Apoll011/Lambda-One/hardware/Lambda One.kicad_sch

## KiCad design hardware/Lambda One.kicad_sch (2026-07-18)

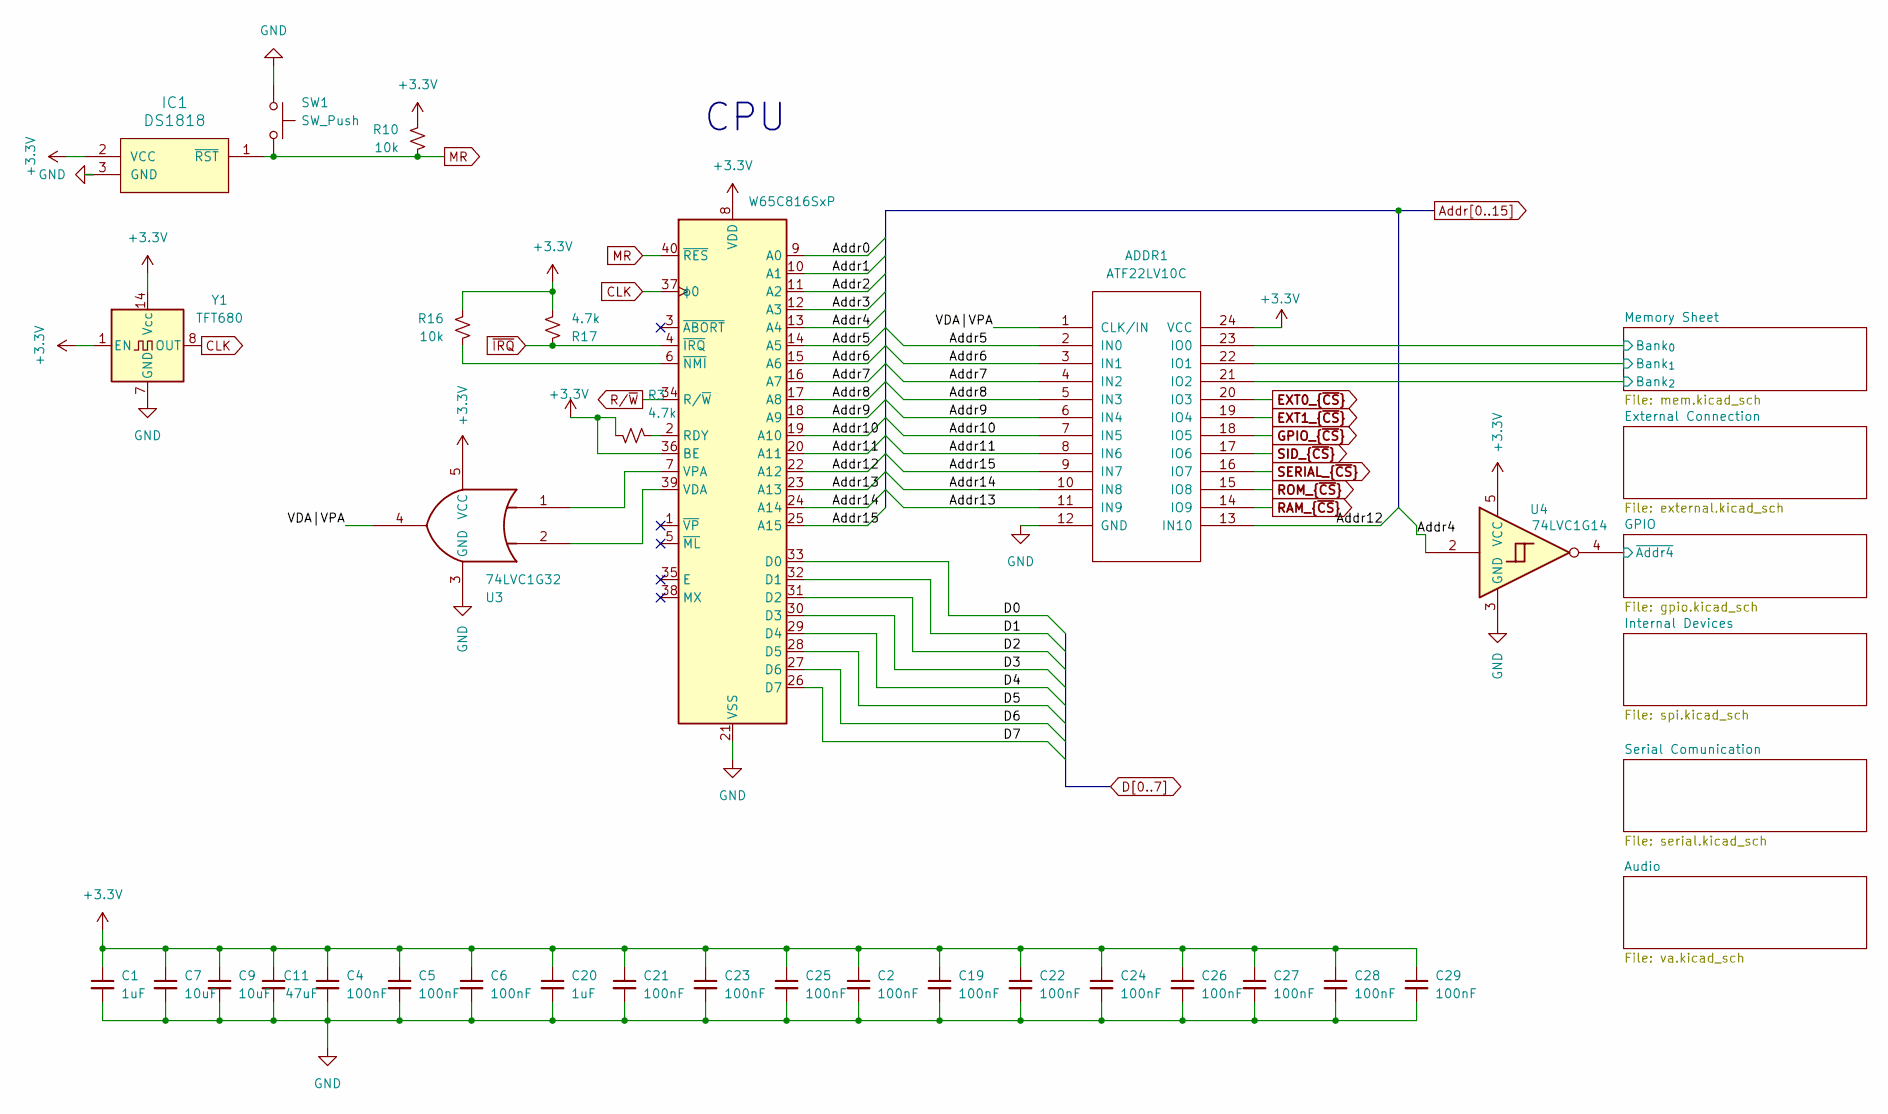
[picture p9: schematic Lambda One.kicad_sch]

Parts:
ADDR1: ATF22LV10C; DIP-24_W7.62mm
C1, C20: 1uF; C_0603_1608Metric; PartNumber CL10A105KB8NNNC
C2, C4, C5, C6, C19, C21, C22, C23, C24, C25, C26, C27, C28, C29: 100nF; C_0603_1608Metric; PartNumber CL10B104KB8NNNC
C7, C9: 10uF; C_0603_1608Metric; PartNumber CL10A105KB8NNNC
C11: 47uF; C_0603_1608Metric; PartNumber CL10A105KB8NNNC
CPU1: W65C816SxP; DIP-40_W15.24mm
IC1: DS1818; TO92127P495H695-3
R3, R17: 4.7k; R_0603_1608Metric; PartNumber AC0603JR-0710KL
R10, R16: 10k; R_0603_1608Metric; PartNumber AC0603JR-0710KL
SW1: SW_Push; SW_Push_1P1T_NO_CK_PTS125Sx73PSMTR
U3: 74LVC1G32; SOT-23-5
U4: 74LVC1G14; SOT-23-5
Y1: TFT680; Oscillator_DIP-14

Connections:
+3.3V: ADDR1.24 (VCC), C1.1, C2.1, C4.1, C5.1, C6.1, C7.1, C9.1, C11.1, C19.1, C20.1, C21.1, C22.1, C23.1, C24.1, C25.1, C26.1, C27.1, C28.1, C29.1, CPU1.8 (VDD), CPU1.36 (BE), IC1.2 (VCC), R3.2, R10.1, R16.1, R17.2, U3.5 (VCC), U4.5 (VCC), Y1.1 (EN), Y1.14 (Vcc)
Addr0: CPU1.9 (A0)
Addr1: CPU1.10 (A1)
Addr2: CPU1.11 (A2)
Addr3: CPU1.12 (A3)
Addr4: CPU1.13 (A4), U4.2
Addr5: ADDR1.2 (IN0), CPU1.14 (A5)
Addr6: ADDR1.3 (IN1), CPU1.15 (A6)
Addr7: ADDR1.4 (IN2), CPU1.16 (A7)
Addr8: ADDR1.5 (IN3), CPU1.17 (A8)
Addr9: ADDR1.6 (IN4), CPU1.18 (A9)
Addr10: ADDR1.7 (IN5), CPU1.19 (A10)
Addr11: ADDR1.8 (IN6), CPU1.20 (A11)
Addr12: ADDR1.13 (IN10), CPU1.22 (A12)
Addr13: ADDR1.11 (IN9), CPU1.23 (A13)
Addr14: ADDR1.10 (IN8), CPU1.24 (A14)
Addr15: ADDR1.9 (IN7), CPU1.25 (A15)
Bank_{0}: ADDR1.23 (IO0)
Bank_{1}: ADDR1.22 (IO1)
Bank_{2}: ADDR1.21 (IO2)
CLK: CPU1.37 (ϕ0), Y1.8 (OUT)
D0: CPU1.33 (D0)
D1: CPU1.32 (D1)
D2: CPU1.31 (D2)
D3: CPU1.30 (D3)
D4: CPU1.29 (D4)
D5: CPU1.28 (D5)
D6: CPU1.27 (D6)
D7: CPU1.26 (D7)
EXT0_{~CS}: ADDR1.20 (IO3)
EXT1_{~CS}: ADDR1.19 (IO4)
GND: ADDR1.12 (GND), C1.2, C2.2, C4.2, C5.2, C6.2, C7.2, C9.2, C11.2, C19.2, C20.2, C21.2, C22.2, C23.2, C24.2, C25.2, C26.2, C27.2, C28.2, C29.2, CPU1.21 (VSS), IC1.3 (GND), SW1.1, U3.3 (GND), U4.3 (GND), Y1.7 (GND)
GPIO_{~CS}: ADDR1.18 (IO5)
MR: CPU1.40 (~RES), IC1.1 (~RST), R10.2, SW1.2
unnamed: CPU1.2 (RDY), R3.1
unnamed: CPU1.6 (~NMI), R16.2
unnamed: CPU1.7 (VPA), U3.1
unnamed: CPU1.39 (VDA), U3.2
RAM_{~CS}: ADDR1.14 (IO9)
ROM_{~CS}: ADDR1.15 (IO8)
R/~W: CPU1.34 (R/~W)
SERIAL_{~CS}: ADDR1.16 (IO7)
SID_{~CS}: ADDR1.17 (IO6)
VDA|VPA: ADDR1.1 (CLK/IN), U3.4
~Addr4: U4.4
~IRQ: CPU1.4 (~IRQ), R17.1

Notes on the sheet:
CPU
