Apoll011/Lambda-One/hardware/ethernet.kicad_sch

## KiCad design hardware/ethernet.kicad_sch (2026-07-13)

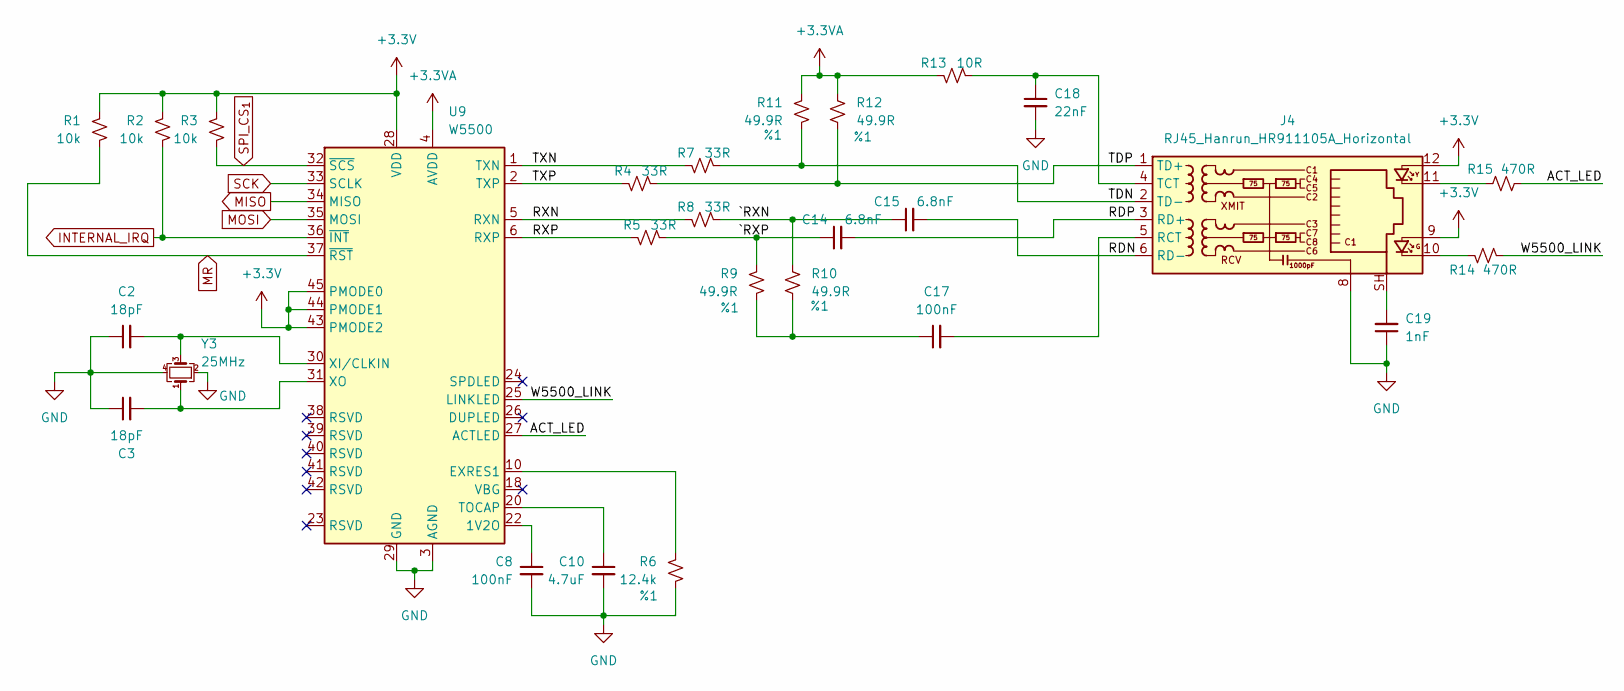
[picture p10: schematic ethernet.kicad_sch]

Parts:
C2, C3: 18pF; C_0603_1608Metric; PartNumber CC0603JRNPO9BN180
C8, C17: 100nF; C_0603_1608Metric; PartNumber CL10B104KB8NNNC
C10: 4.7uF; C_0603_1608Metric; PartNumber CL10B475KQ8NQNC
C14, C15: 6.8nF; C_0603_1608Metric; PartNumber CL10B682KB8NNNC
C18: 22nF; C_0603_1608Metric; PartNumber CL10B223KB8NNNC
C19: 1nF; C_1210_3225Metric; PartNumber CL32B102KJFNNNE
J4: RJ45_Hanrun_HR911105A_Horizontal; PartNumber HR911105A
R1, R2, R3: 10k; R_0603_1608Metric; PartNumber AC0603JR-0710KL
R4, R5, R7, R8: 33R; R_0603_1608Metric; PartNumber RC0603JR-0733RL
R6: 12.4k; R_0603_1608Metric; Tolerance %1; PartNumber RC0603FR-0712K4L
R9, R10, R11, R12: 49.9R; R_0603_1608Metric; Tolerance %1; PartNumber ERA-3AEB49R9V
R13: 10R; R_0603_1608Metric; PartNumber RC0603FR-0710RL
R14, R15: 470R; R_0603_1608Metric; PartNumber RC0603JR-07470RL
U9: W5500; LQFP-48_7x7mm_P0.5mm; PartNumber W5500
Y3: 25MHz; Crystal_SMD_Abracon_ABM8AIG-4Pin_3.2x2.5mm; PartNumber RH100-25.000-10-F-2030-E

Connections:
+3.3V: J4.9, J4.12, R1.1, R2.1, R3.1, U9.28 (VDD), U9.43 (PMODE2), U9.44 (PMODE1), U9.45 (PMODE0)
+3.3VA: R11.1, R12.1, R13.1, U9.4 (AVDD), U9.8 (AVDD), U9.11 (AVDD), U9.15 (AVDD), U9.17 (AVDD), U9.21 (AVDD)
ACT_LED: R15.2, U9.27 (ACTLED)
GND: C2.1, C3.1, C8.2, C10.2, C18.2, C19.1, J4.8, R6.2, U9.3 (AGND), U9.9 (AGND), U9.14 (AGND), U9.16 (AGND), U9.19 (AGND), U9.29 (GND), U9.48 (AGND), Y3.2, Y3.4
INTERNAL_IRQ: R2.2, U9.36 (~INT)
MISO: U9.34 (MISO)
MOSI: U9.35 (MOSI)
MR: R1.2, U9.37 (~RST)
unnamed: C2.2, U9.30 (XI/CLKIN), Y3.3
unnamed: C3.2, U9.31 (XO), Y3.1
unnamed: C8.1, U9.22 (1V2O)
unnamed: C10.1, U9.20 (TOCAP)
unnamed: C17.1, R9.2, R10.2
unnamed: C17.2, J4.5 (RCT)
unnamed: C18.1, J4.4 (TCT), R13.2
unnamed: C19.2, J4.SH
unnamed: J4.10, R14.1
unnamed: J4.11, R15.1
unnamed: R6.1, U9.10 (EXRES1)
RDN: C15.2, J4.6 (RD-)
RDP: C14.2, J4.3 (RD+)
RXN: R8.1, U9.5 (RXN)
RXP: R5.1, U9.6 (RXP)
SCK: U9.33 (SCLK)
SPI_CS_{1}: R3.2, U9.32 (~SCS)
TDN: J4.2 (TD-), R7.2, R11.2
TDP: J4.1 (TD+), R4.2, R12.2
TXN: R7.1, U9.1 (TXN)
TXP: R4.1, U9.2 (TXP)
W5500_LINK: R14.2, U9.25 (LINKLED)
`RXN: C15.1, R8.2, R10.1
`RXP: C14.1, R5.2, R9.1
