Apoll011/Lambda-One/hardware/external.kicad_sch

## KiCad design hardware/external.kicad_sch (2026-07-18)

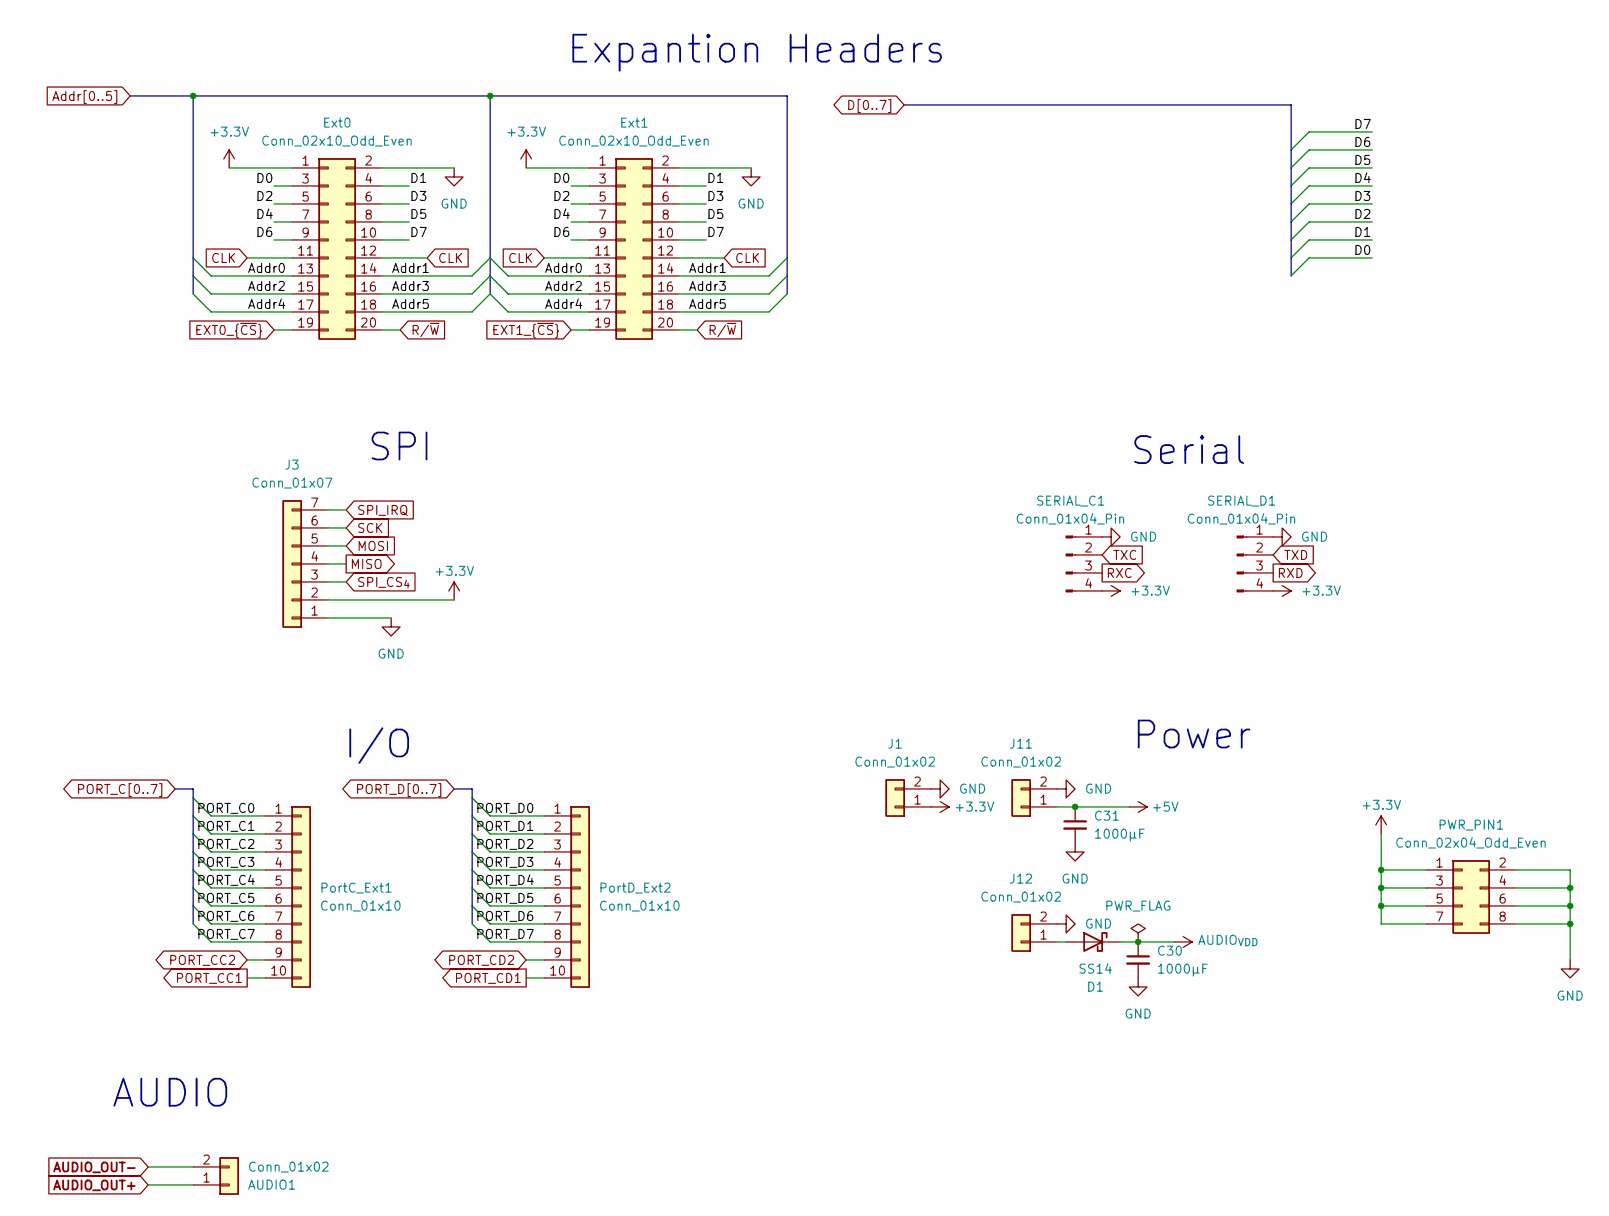
[picture p11: schematic external.kicad_sch]

Parts:
AUDIO1: Conn_01x02; JST_XH_B2B-XH-A_1x02_P2.50mm_Vertical
C30, C31: 1000µF; Fuse_Bourns_MF-RG1000; PartNumber CL10B104KB8NNNC
D1: SS14; D_SMA
Ext0, Ext1: Conn_02x10_Odd_Even; IDC-Header_2x10_P2.54mm_Vertical
J1, J11, J12: Conn_01x02; JST_XH_B2B-XH-A_1x02_P2.50mm_Vertical
J3: Conn_01x07; PinHeader_1x07_P2.54mm_Vertical
PWR_PIN1: Conn_02x04_Odd_Even; PinHeader_2x04_P2.54mm_Vertical
PortC_Ext1: Conn_01x10; PinHeader_1x10_P2.54mm_Vertical
PortD_Ext2: Conn_01x10; PinHeader_1x10_P2.54mm_Vertical
SERIAL_C1: Conn_01x04_Pin; PinHeader_1x04_P2.54mm_Vertical
SERIAL_D1: Conn_01x04_Pin; PinHeader_1x04_P2.54mm_Vertical

Connections:
+3.3V: Ext0.1, Ext1.1, J1.1, J3.2, PWR_PIN1.1, PWR_PIN1.3, PWR_PIN1.5, PWR_PIN1.7, SERIAL_C1.4, SERIAL_D1.4
+5V: C31.1, J11.1
AUDIO_OUT+: AUDIO1.1
AUDIO_OUT-: AUDIO1.2
AUDIO_{VDD}: C30.1, D1.1 (K)
Addr0: Ext0.13, Ext1.13
Addr1: Ext0.14, Ext1.14
Addr2: Ext0.15, Ext1.15
Addr3: Ext0.16, Ext1.16
Addr4: Ext0.17, Ext1.17
Addr5: Ext0.18, Ext1.18
CLK: Ext0.11, Ext0.12, Ext1.11, Ext1.12
D0: Ext0.3, Ext1.3
D1: Ext0.4, Ext1.4
D2: Ext0.5, Ext1.5
D3: Ext0.6, Ext1.6
D4: Ext0.7, Ext1.7
D5: Ext0.8, Ext1.8
D6: Ext0.9, Ext1.9
D7: Ext0.10, Ext1.10
EXT0_{~CS}: Ext0.19
EXT1_{~CS}: Ext1.19
GND: C30.2, C31.2, Ext0.2, Ext1.2, J1.2, J3.1, J11.2, J12.2, PWR_PIN1.2, PWR_PIN1.4, PWR_PIN1.6, PWR_PIN1.8, SERIAL_C1.1, SERIAL_D1.1
MISO: J3.4
MOSI: J3.5
unnamed: D1.2 (A), J12.1
PORT_C0: PortC_Ext1.1
PORT_C1: PortC_Ext1.2
PORT_C2: PortC_Ext1.3
PORT_C3: PortC_Ext1.4
PORT_C4: PortC_Ext1.5
PORT_C5: PortC_Ext1.6
PORT_C6: PortC_Ext1.7
PORT_C7: PortC_Ext1.8
PORT_CC1: PortC_Ext1.10
PORT_CC2: PortC_Ext1.9
PORT_CD1: PortD_Ext2.10
PORT_CD2: PortD_Ext2.9
PORT_D0: PortD_Ext2.1
PORT_D1: PortD_Ext2.2
PORT_D2: PortD_Ext2.3
PORT_D3: PortD_Ext2.4
PORT_D4: PortD_Ext2.5
PORT_D5: PortD_Ext2.6
PORT_D6: PortD_Ext2.7
PORT_D7: PortD_Ext2.8
RXC: SERIAL_C1.3
RXD: SERIAL_D1.3
R/~W: Ext0.20, Ext1.20
SCK: J3.6
SPI_CS_{4}: J3.3
SPI_IRQ: J3.7
TXC: SERIAL_C1.2
TXD: SERIAL_D1.2

Notes on the sheet:
Power
SPI
Expantion Headers
Serial
I/O
AUDIO
