Apoll011/Lambda-One/hardware/gpio.kicad_sch

## KiCad design hardware/gpio.kicad_sch (2026-07-18)

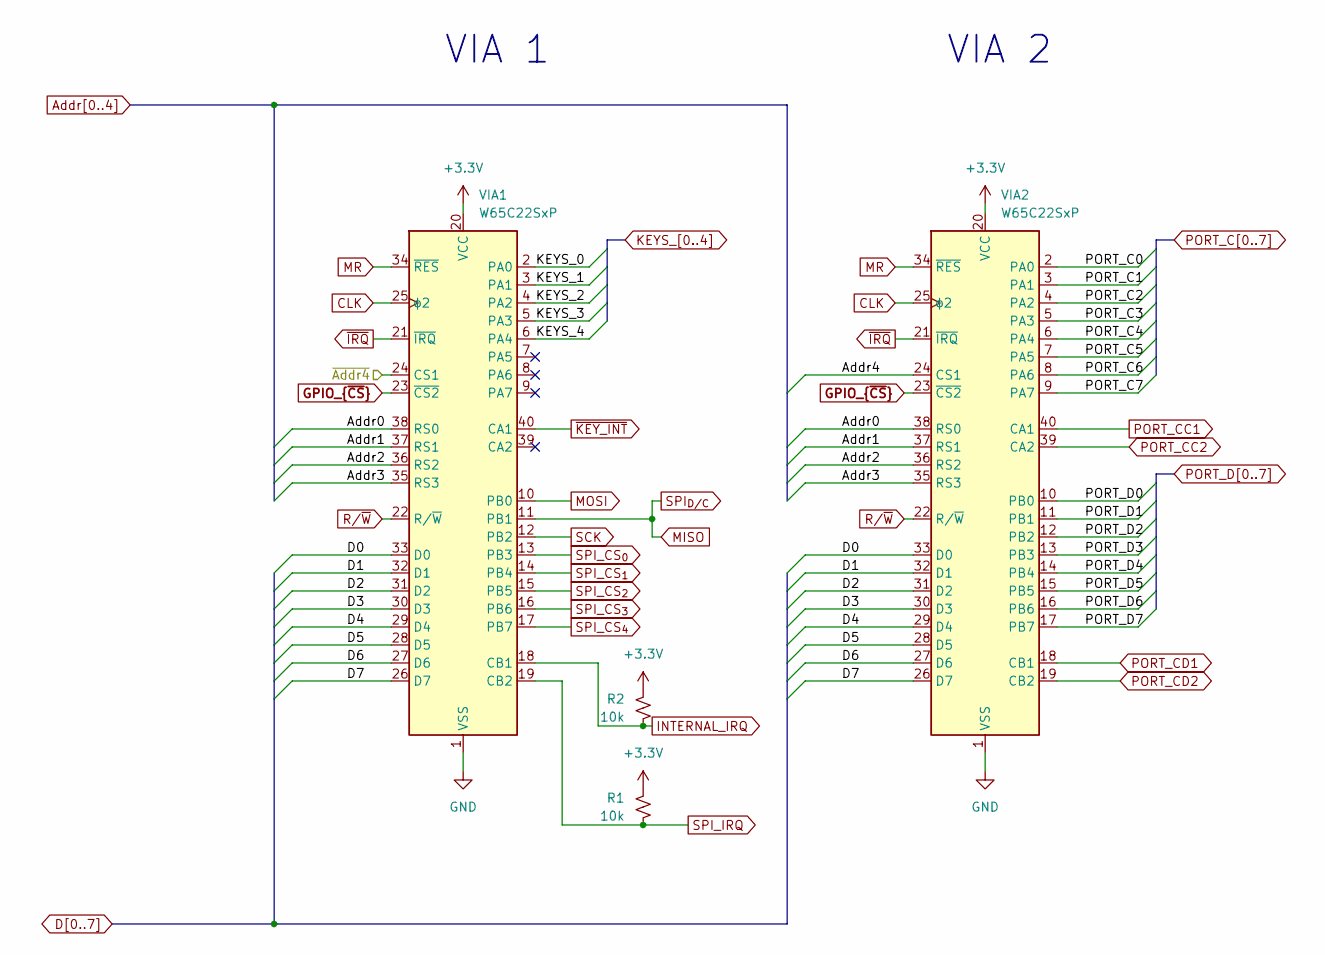
[picture p12: schematic gpio.kicad_sch]

Parts:
R1, R2: 10k; R_0603_1608Metric; PartNumber AC0603JR-0710KL
VIA1, VIA2: W65C22SxP; DIP-40_W15.24mm

Connections:
+3.3V: R1.1, R2.1, VIA1.20 (VCC), VIA2.20 (VCC)
Addr0: VIA1.38 (RS0), VIA2.38 (RS0)
Addr1: VIA1.37 (RS1), VIA2.37 (RS1)
Addr2: VIA1.36 (RS2), VIA2.36 (RS2)
Addr3: VIA1.35 (RS3), VIA2.35 (RS3)
Addr4: VIA2.24 (CS1)
CLK: VIA1.25 (ϕ2), VIA2.25 (ϕ2)
D0: VIA1.33 (D0), VIA2.33 (D0)
D1: VIA1.32 (D1), VIA2.32 (D1)
D2: VIA1.31 (D2), VIA2.31 (D2)
D3: VIA1.30 (D3), VIA2.30 (D3)
D4: VIA1.29 (D4), VIA2.29 (D4)
D5: VIA1.28 (D5), VIA2.28 (D5)
D6: VIA1.27 (D6), VIA2.27 (D6)
D7: VIA1.26 (D7), VIA2.26 (D7)
GND: VIA1.1 (VSS), VIA2.1 (VSS)
GPIO_{~CS}: VIA1.23 (~CS2), VIA2.23 (~CS2)
INTERNAL_IRQ: R2.2, VIA1.18 (CB1)
KEYS_0: VIA1.2 (PA0)
KEYS_1: VIA1.3 (PA1)
KEYS_2: VIA1.4 (PA2)
KEYS_3: VIA1.5 (PA3)
KEYS_4: VIA1.6 (PA4)
MISO: VIA1.11 (PB1)
MOSI: VIA1.10 (PB0)
MR: VIA1.34 (~RES), VIA2.34 (~RES)
PORT_C0: VIA2.2 (PA0)
PORT_C1: VIA2.3 (PA1)
PORT_C2: VIA2.4 (PA2)
PORT_C3: VIA2.5 (PA3)
PORT_C4: VIA2.6 (PA4)
PORT_C5: VIA2.7 (PA5)
PORT_C6: VIA2.8 (PA6)
PORT_C7: VIA2.9 (PA7)
PORT_CC1: VIA2.40 (CA1)
PORT_CC2: VIA2.39 (CA2)
PORT_CD1: VIA2.18 (CB1)
PORT_CD2: VIA2.19 (CB2)
PORT_D0: VIA2.10 (PB0)
PORT_D1: VIA2.11 (PB1)
PORT_D2: VIA2.12 (PB2)
PORT_D3: VIA2.13 (PB3)
PORT_D4: VIA2.14 (PB4)
PORT_D5: VIA2.15 (PB5)
PORT_D6: VIA2.16 (PB6)
PORT_D7: VIA2.17 (PB7)
R/~W: VIA1.22 (R/~W), VIA2.22 (R/~W)
SCK: VIA1.12 (PB2)
SPI_CS_{0}: VIA1.13 (PB3)
SPI_CS_{1}: VIA1.14 (PB4)
SPI_CS_{2}: VIA1.15 (PB5)
SPI_CS_{3}: VIA1.16 (PB6)
SPI_CS_{4}: VIA1.17 (PB7)
SPI_IRQ: R1.2, VIA1.19 (CB2)
~Addr4: VIA1.24 (CS1)
~IRQ: VIA1.21 (~IRQ), VIA2.21 (~IRQ)
~KEY_INT: VIA1.40 (CA1)

Notes on the sheet:
VIA 1
VIA 2
