Apoll011/Lambda-One/hardware/interface.kicad_sch

## KiCad design hardware/interface.kicad_sch (2026-07-13)

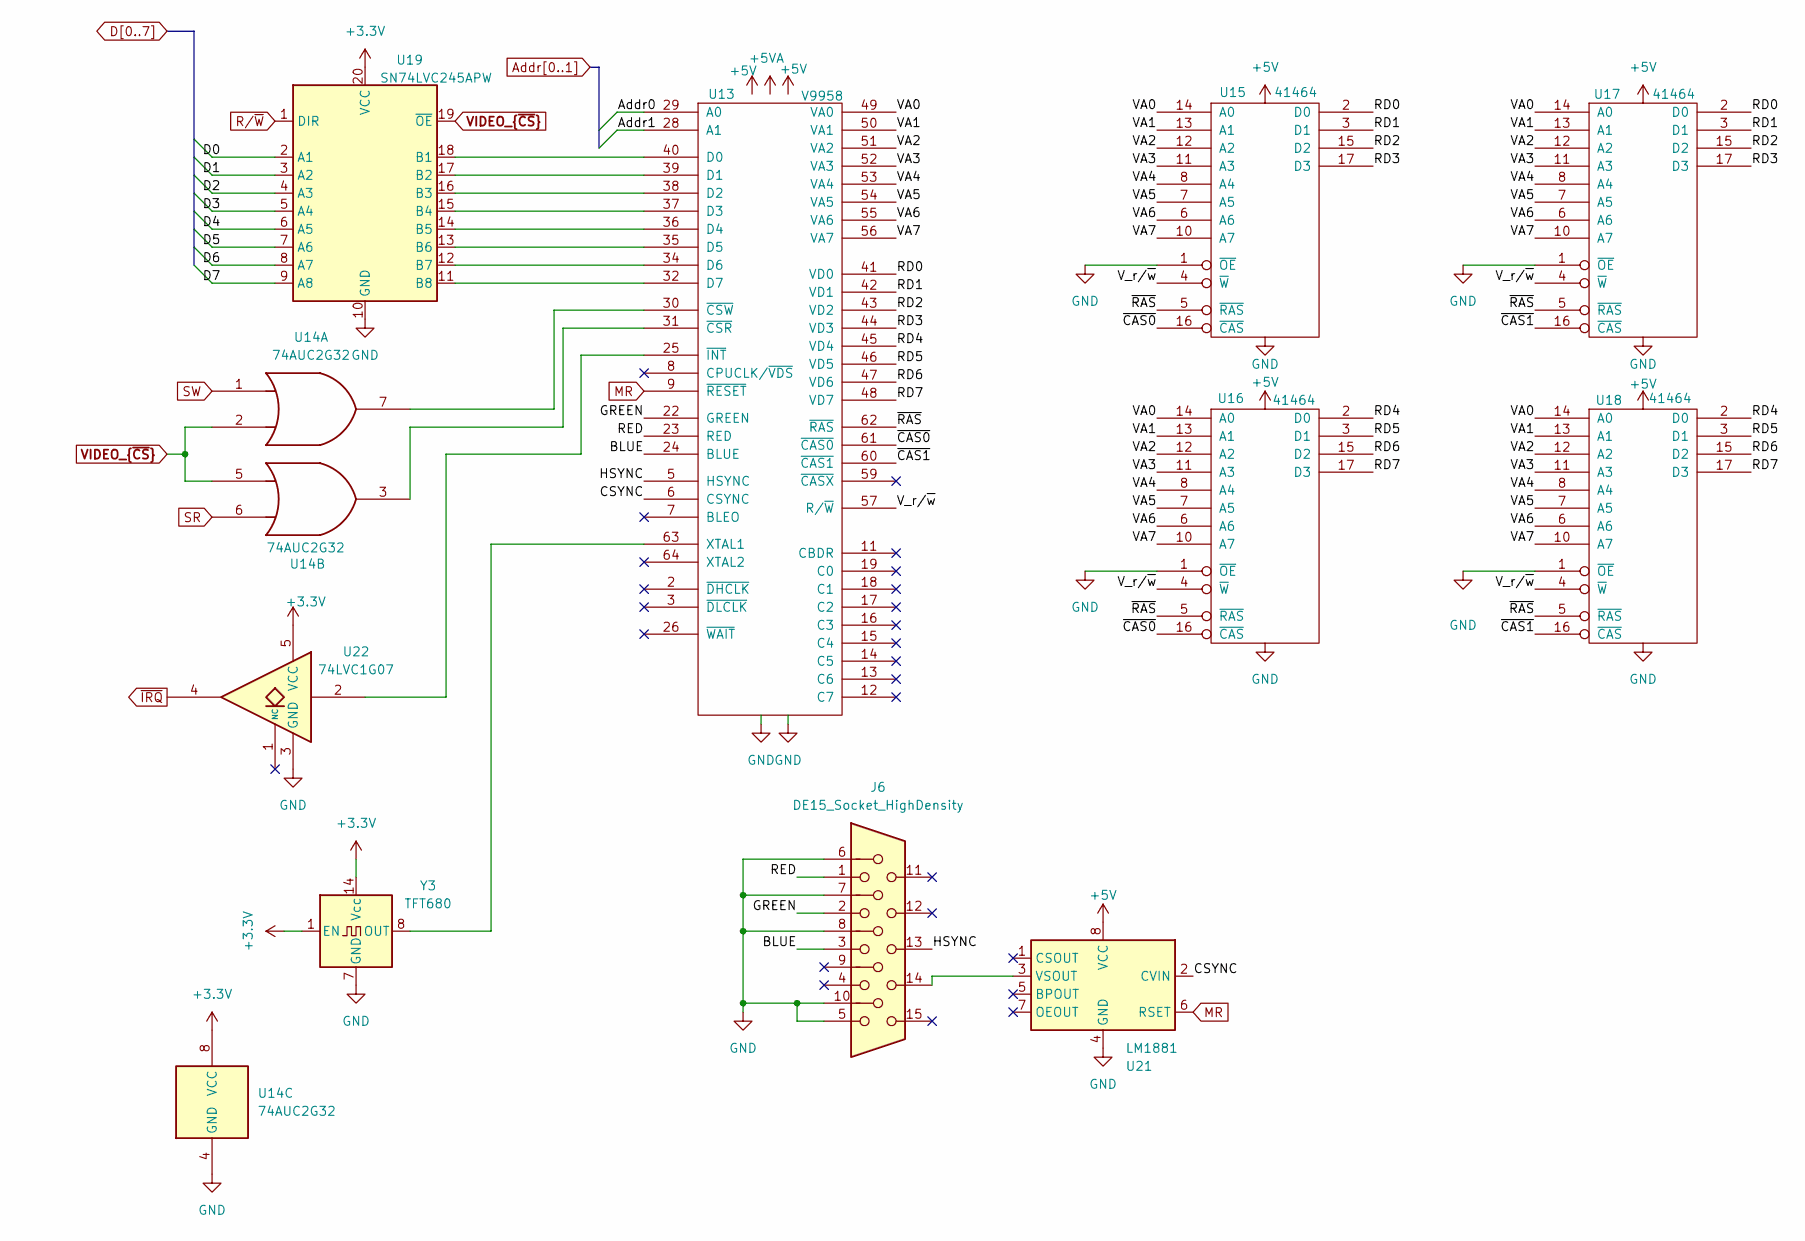
[picture p13: schematic interface.kicad_sch]

Parts:
J6: DE15_Socket_HighDensity
U13: V9958
U14: 74AUC2G32
U15, U16, U17, U18: 41464
U19: SN74LVC245APW; TSSOP-20_4.4x6.5mm_P0.65mm
U21: LM1881
U22: 74LVC1G07
Y3: TFT680; Oscillator_DIP-14

Connections:
+3.3V: U14.8 (VCC), U19.20 (VCC), U22.5 (VCC), Y3.1 (EN), Y3.14 (Vcc)
+5V: U13.33 (Vbb), U13.58 (VCC), U15.9 (VCC), U16.9 (VCC), U17.9 (VCC), U18.9 (VCC), U21.8 (VCC)
+5VA: U13.21 (VDD)
Addr0: U13.29 (A0)
Addr1: U13.28 (A1)
BLUE: J6.3, U13.24 (BLUE)
CSYNC: U13.6 (CSYNC), U21.2 (CVIN)
D0: U19.2 (A1)
D1: U19.3 (A2)
D2: U19.4 (A3)
D3: U19.5 (A4)
D4: U19.6 (A5)
D5: U19.7 (A6)
D6: U19.8 (A7)
D7: U19.9 (A8)
GND: J6.5, J6.6, J6.7, J6.8, J6.10, U13.1 (GND), U13.20 (GND), U14.4 (GND), U15.1 (~OE), U15.18 (GND), U16.1 (~OE), U16.18 (GND), U17.1 (~OE), U17.18 (GND), U18.1 (~OE), U18.18 (GND), U19.10 (GND), U21.4 (GND), U22.3 (GND), Y3.7 (GND)
GREEN: J6.2, U13.22 (GREEN)
HSYNC: J6.13, U13.5 (HSYNC)
MR: U13.9 (~RESET), U21.6 (RSET)
unnamed: J6.14, U21.3 (VSOUT)
unnamed: U13.25 (~INT), U22.2
unnamed: U13.30 (~CSW), U14.7
unnamed: U13.31 (~CSR), U14.3
unnamed: U13.32 (D7), U19.11 (B8)
unnamed: U13.34 (D6), U19.12 (B7)
unnamed: U13.35 (D5), U19.13 (B6)
unnamed: U13.36 (D4), U19.14 (B5)
unnamed: U13.37 (D3), U19.15 (B4)
unnamed: U13.38 (D2), U19.16 (B3)
unnamed: U13.39 (D1), U19.17 (B2)
unnamed: U13.40 (D0), U19.18 (B1)
unnamed: U13.63 (XTAL1), Y3.8 (OUT)
RD0: U13.41 (VD0), U15.2 (D0), U17.2 (D0)
RD1: U13.42 (VD1), U15.3 (D1), U17.3 (D1)
RD2: U13.43 (VD2), U15.15 (D2), U17.15 (D2)
RD3: U13.44 (VD3), U15.17 (D3), U17.17 (D3)
RD4: U13.45 (VD4), U16.2 (D0), U18.2 (D0)
RD5: U13.46 (VD5), U16.3 (D1), U18.3 (D1)
RD6: U13.47 (VD6), U16.15 (D2), U18.15 (D2)
RD7: U13.48 (VD7), U16.17 (D3), U18.17 (D3)
RED: J6.1, U13.23 (RED)
R/~W: U19.1 (DIR)
SR: U14.6
SW: U14.1
VA0: U13.49 (VA0), U15.14 (A0), U16.14 (A0), U17.14 (A0), U18.14 (A0)
VA1: U13.50 (VA1), U15.13 (A1), U16.13 (A1), U17.13 (A1), U18.13 (A1)
VA2: U13.51 (VA2), U15.12 (A2), U16.12 (A2), U17.12 (A2), U18.12 (A2)
VA3: U13.52 (VA3), U15.11 (A3), U16.11 (A3), U17.11 (A3), U18.11 (A3)
VA4: U13.53 (VA4), U15.8 (A4), U16.8 (A4), U17.8 (A4), U18.8 (A4)
VA5: U13.54 (VA5), U15.7 (A5), U16.7 (A5), U17.7 (A5), U18.7 (A5)
VA6: U13.55 (VA6), U15.6 (A6), U16.6 (A6), U17.6 (A6), U18.6 (A6)
VA7: U13.56 (VA7), U15.10 (A7), U16.10 (A7), U17.10 (A7), U18.10 (A7)
VIDEO_{~CS}: U14.2, U14.5, U19.19 (~OE)
V_r/~w: U13.57 (R/~W), U15.4 (~W), U16.4 (~W), U17.4 (~W), U18.4 (~W)
~CAS0: U13.61 (~CAS0), U15.16 (~CAS), U16.16 (~CAS)
~CAS1: U13.60 (~CAS1), U17.16 (~CAS), U18.16 (~CAS)
~IRQ: U22.4
~RAS: U13.62 (~RAS), U15.5 (~RAS), U16.5 (~RAS), U17.5 (~RAS), U18.5 (~RAS)
