Apoll011/Lambda-One/hardware/mem.kicad_sch

## KiCad design hardware/mem.kicad_sch (2026-07-18)

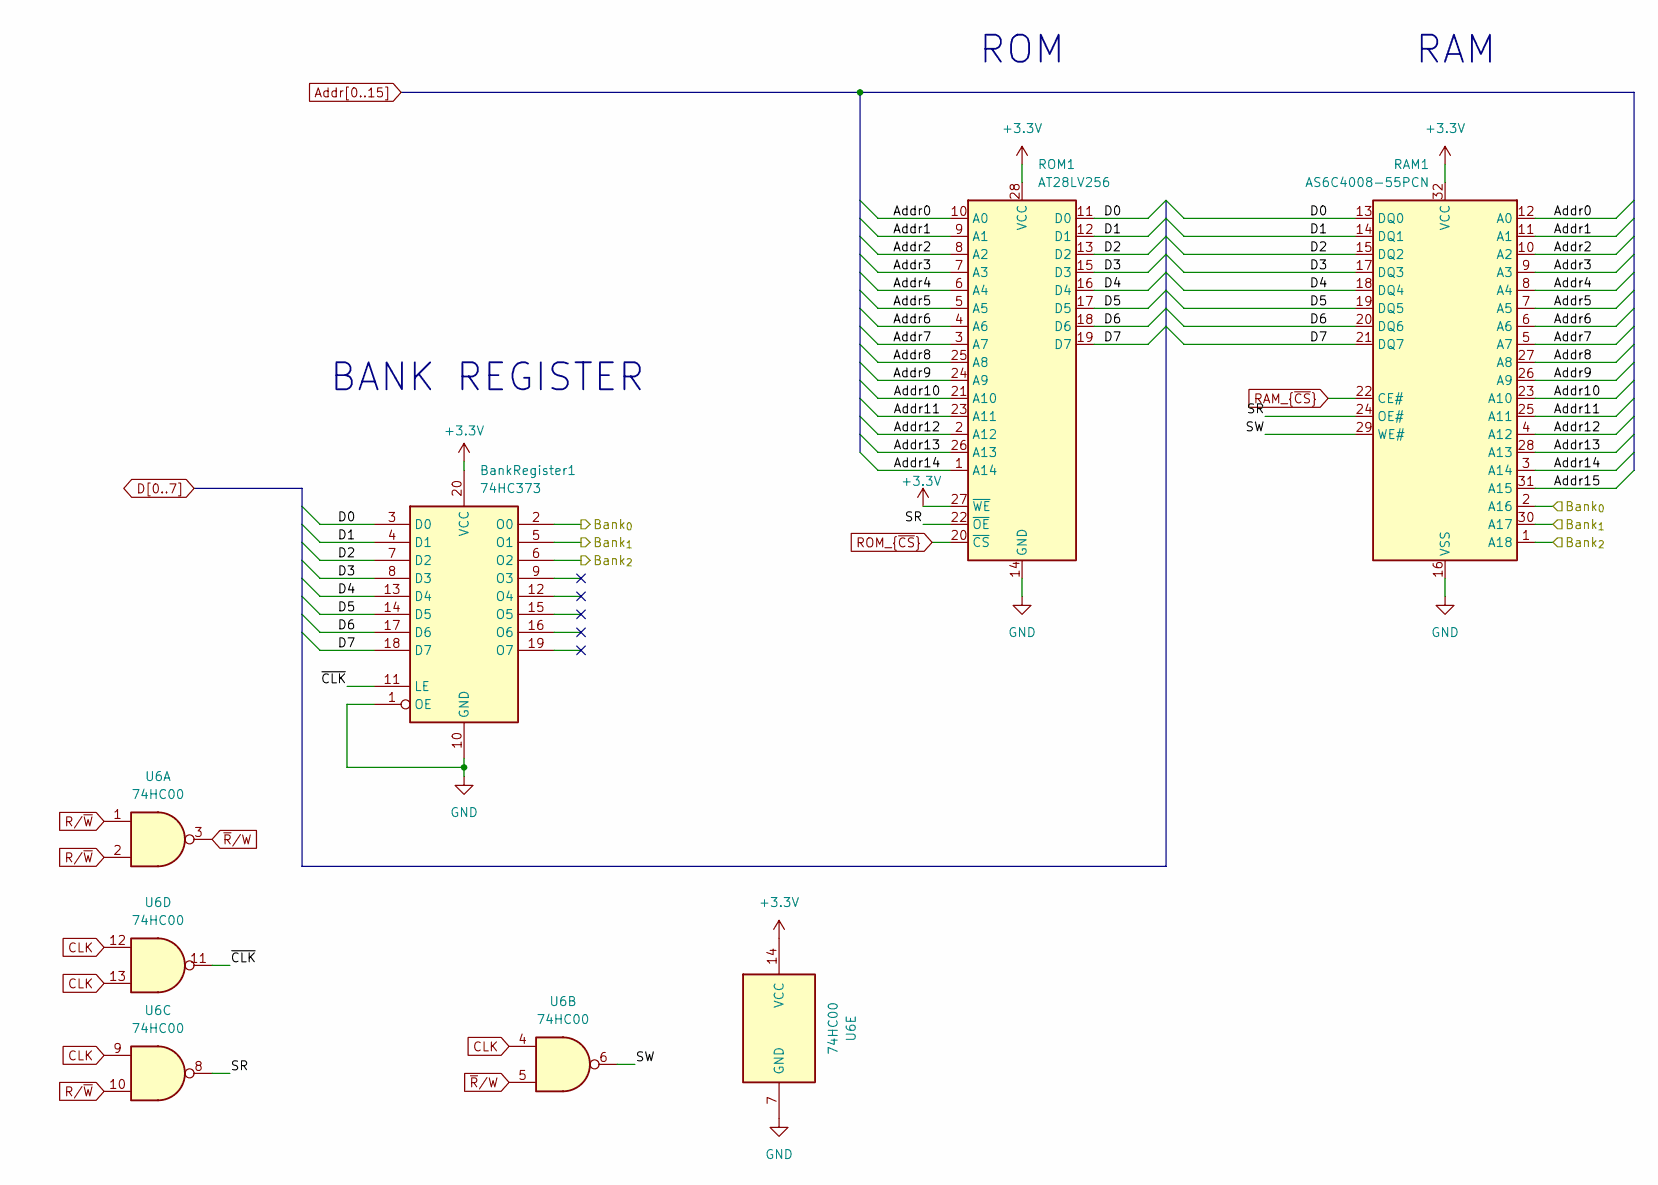
[picture p14: schematic mem.kicad_sch]

Parts:
BankRegister1: 74HC373; DIP-20_W7.62mm
RAM1: AS6C4008-55PCN; DIP-32_W15.24mm
ROM1: AT28LV256; DIP-28_W15.24mm_Socket
U6: 74HC00; DIP-14_W7.62mm

Connections:
+3.3V: BankRegister1.20 (VCC), RAM1.32 (VCC), ROM1.27 (~WE), ROM1.28 (VCC), U6.14 (VCC)
Addr0: RAM1.12 (A0), ROM1.10 (A0)
Addr1: RAM1.11 (A1), ROM1.9 (A1)
Addr2: RAM1.10 (A2), ROM1.8 (A2)
Addr3: RAM1.9 (A3), ROM1.7 (A3)
Addr4: RAM1.8 (A4), ROM1.6 (A4)
Addr5: RAM1.7 (A5), ROM1.5 (A5)
Addr6: RAM1.6 (A6), ROM1.4 (A6)
Addr7: RAM1.5 (A7), ROM1.3 (A7)
Addr8: RAM1.27 (A8), ROM1.25 (A8)
Addr9: RAM1.26 (A9), ROM1.24 (A9)
Addr10: RAM1.23 (A10), ROM1.21 (A10)
Addr11: RAM1.25 (A11), ROM1.23 (A11)
Addr12: RAM1.4 (A12), ROM1.2 (A12)
Addr13: RAM1.28 (A13), ROM1.26 (A13)
Addr14: RAM1.3 (A14), ROM1.1 (A14)
Addr15: RAM1.31 (A15)
Bank_{0}: BankRegister1.2 (O0), RAM1.2 (A16)
Bank_{1}: BankRegister1.5 (O1), RAM1.30 (A17)
Bank_{2}: BankRegister1.6 (O2), RAM1.1 (A18)
CLK: U6.4, U6.9, U6.12, U6.13
D0: BankRegister1.3 (D0), RAM1.13 (DQ0), ROM1.11 (D0)
D1: BankRegister1.4 (D1), RAM1.14 (DQ1), ROM1.12 (D1)
D2: BankRegister1.7 (D2), RAM1.15 (DQ2), ROM1.13 (D2)
D3: BankRegister1.8 (D3), RAM1.17 (DQ3), ROM1.15 (D3)
D4: BankRegister1.13 (D4), RAM1.18 (DQ4), ROM1.16 (D4)
D5: BankRegister1.14 (D5), RAM1.19 (DQ5), ROM1.17 (D5)
D6: BankRegister1.17 (D6), RAM1.20 (DQ6), ROM1.18 (D6)
D7: BankRegister1.18 (D7), RAM1.21 (DQ7), ROM1.19 (D7)
GND: BankRegister1.1 (OE), BankRegister1.10 (GND), RAM1.16 (VSS), ROM1.14 (GND), U6.7 (GND)
RAM_{~CS}: RAM1.22 (CE#)
ROM_{~CS}: ROM1.20 (~CS)
R/~W: U6.1, U6.2, U6.10
SR: RAM1.24 (OE#), ROM1.22 (~OE), U6.8
SW: RAM1.29 (WE#), U6.6
~CLK: BankRegister1.11 (LE), U6.11
~R/W: U6.3, U6.5

Notes on the sheet:
RAM
BANK REGISTER
ROM
