Apoll011/Lambda-One/hardware/serial.kicad_sch

## KiCad design hardware/serial.kicad_sch (2026-07-18)

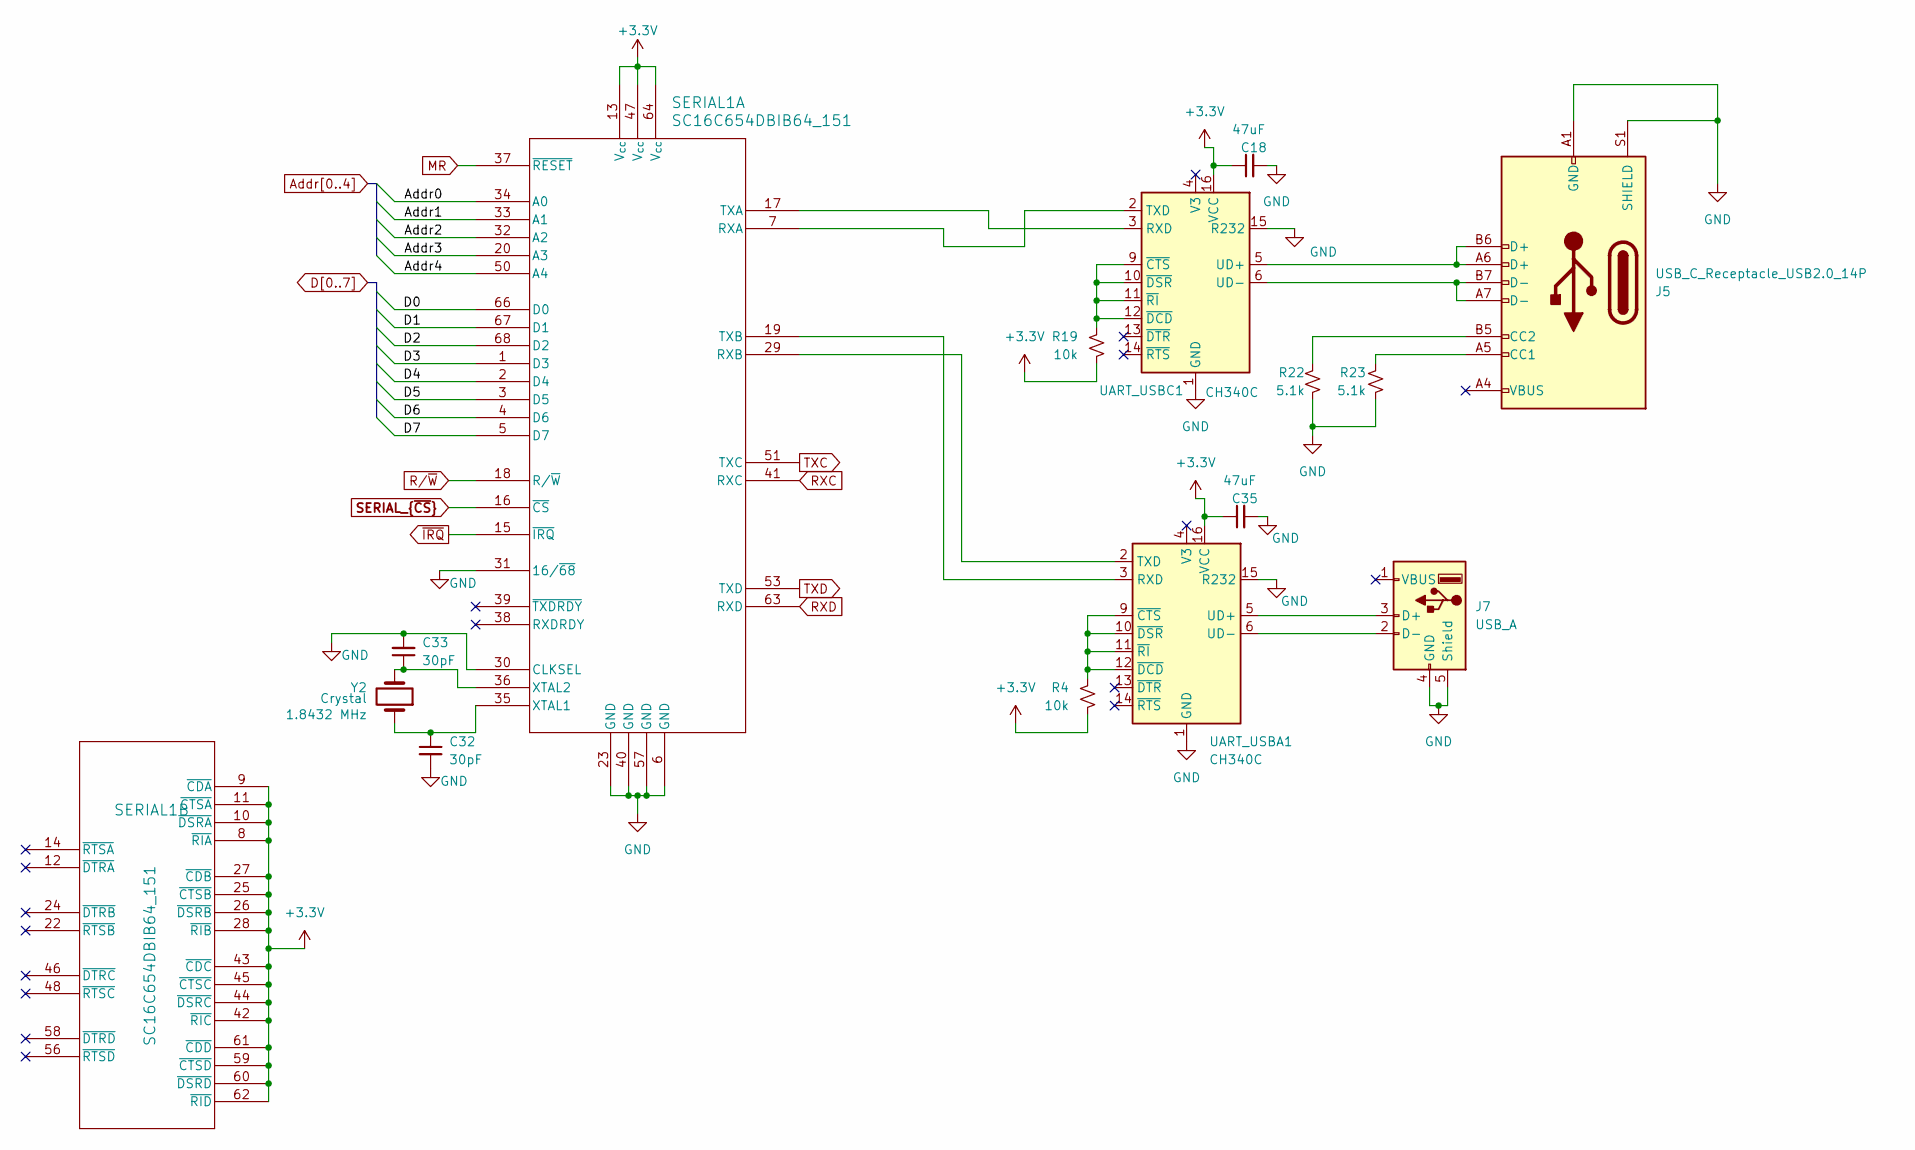
[picture p15: schematic serial.kicad_sch]

Parts:
C18, C35: 47uF; C_0603_1608Metric; PartNumber CL10A105KB8NNNC
C32, C33: 30pF; C_0603_1608Metric; PartNumber CL10B104KB8NNNC
J5: USB_C_Receptacle_USB2.0_14P; USB_C_Receptacle_Amphenol_12401610E4-2A_CircularHoles
J7: USB_A; USB_A_Molex_67643_Horizontal
R4, R19: 10k; R_0603_1608Metric; PartNumber RC0603FR-0712K4L
R22, R23: 5.1k; R_0603_1608Metric; PartNumber RC0603FR-0712K4L
SERIAL1: SC16C654DBIB64_151; PLCC-68
UART_USBA1: CH340C; SOIC-16_3.9x9.9mm_P1.27mm
UART_USBC1: CH340C; SOIC-16_3.9x9.9mm_P1.27mm
Y2: Crystal; Crystal_HC49-U_Vertical

Connections:
+3.3V: C18.1, C35.1, R4.2, R19.2, SERIAL1.8 (~RIA), SERIAL1.9 (~CDA), SERIAL1.10 (~DSRA), SERIAL1.11 (~CTSA), SERIAL1.13 (V_{cc}), SERIAL1.25 (~CTSB), SERIAL1.26 (~DSRB), SERIAL1.27 (~CDB), SERIAL1.28 (~RIB), SERIAL1.42 (~RIC), SERIAL1.43 (~CDC), SERIAL1.44 (~DSRC), SERIAL1.45 (~CTSC), SERIAL1.47 (V_{cc}), SERIAL1.59 (~CTSD), SERIAL1.60 (~DSRD), SERIAL1.61 (~CDD), SERIAL1.62 (~RID), SERIAL1.64 (V_{cc}), UART_USBA1.16 (VCC), UART_USBC1.16 (VCC)
Addr0: SERIAL1.34 (A0)
Addr1: SERIAL1.33 (A1)
Addr2: SERIAL1.32 (A2)
Addr3: SERIAL1.20 (A3)
Addr4: SERIAL1.50 (A4)
D0: SERIAL1.66 (D0)
D1: SERIAL1.67 (D1)
D2: SERIAL1.68 (D2)
D3: SERIAL1.1 (D3)
D4: SERIAL1.2 (D4)
D5: SERIAL1.3 (D5)
D6: SERIAL1.4 (D6)
D7: SERIAL1.5 (D7)
GND: C18.2, C32.2, C33.2, C35.2, J5.A1 (GND), J5.A12 (GND), J5.B1 (GND), J5.B12 (GND), J5.S1 (SHIELD), J7.4 (GND), J7.5 (Shield), R22.2, R23.2, SERIAL1.6 (GND), SERIAL1.23 (GND), SERIAL1.30 (CLKSEL), SERIAL1.31 (16/~68), SERIAL1.40 (GND), SERIAL1.57 (GND), UART_USBA1.1 (GND), UART_USBA1.15 (R232), UART_USBC1.1 (GND), UART_USBC1.15 (R232)
MR: SERIAL1.37 (~RESET)
unnamed: C32.1, SERIAL1.35 (XTAL1), Y2.1
unnamed: C33.1, SERIAL1.36 (XTAL2), Y2.2
unnamed: J5.A4 (VBUS), J5.A9 (VBUS), J5.B4 (VBUS), J5.B9 (VBUS)
unnamed: J5.A5 (CC1), R23.1
unnamed: J5.A6 (D+), J5.B6 (D+), UART_USBC1.5 (UD+)
unnamed: J5.A7 (D-), J5.B7 (D-), UART_USBC1.6 (UD-)
unnamed: J5.B5 (CC2), R22.1
unnamed: J7.2 (D-), UART_USBA1.6 (UD-)
unnamed: J7.3 (D+), UART_USBA1.5 (UD+)
unnamed: R4.1, UART_USBA1.9 (~CTS), UART_USBA1.10 (~DSR), UART_USBA1.11 (~RI), UART_USBA1.12 (~DCD)
unnamed: R19.1, UART_USBC1.9 (~CTS), UART_USBC1.10 (~DSR), UART_USBC1.11 (~RI), UART_USBC1.12 (~DCD)
unnamed: SERIAL1.7 (RXA), UART_USBC1.2 (TXD)
unnamed: SERIAL1.17 (TXA), UART_USBC1.3 (RXD)
unnamed: SERIAL1.19 (TXB), UART_USBA1.3 (RXD)
unnamed: SERIAL1.29 (RXB), UART_USBA1.2 (TXD)
RXC: SERIAL1.41 (RXC)
RXD: SERIAL1.63 (RXD)
R/~W: SERIAL1.18 (R/~W)
SERIAL_{~CS}: SERIAL1.16 (~CS)
TXC: SERIAL1.51 (TXC)
TXD: SERIAL1.53 (TXD)
~IRQ: SERIAL1.15 (~IRQ)
