Apoll011/Lambda-One/hardware/sid.kicad_sch

## KiCad design hardware/sid.kicad_sch (2026-07-14)

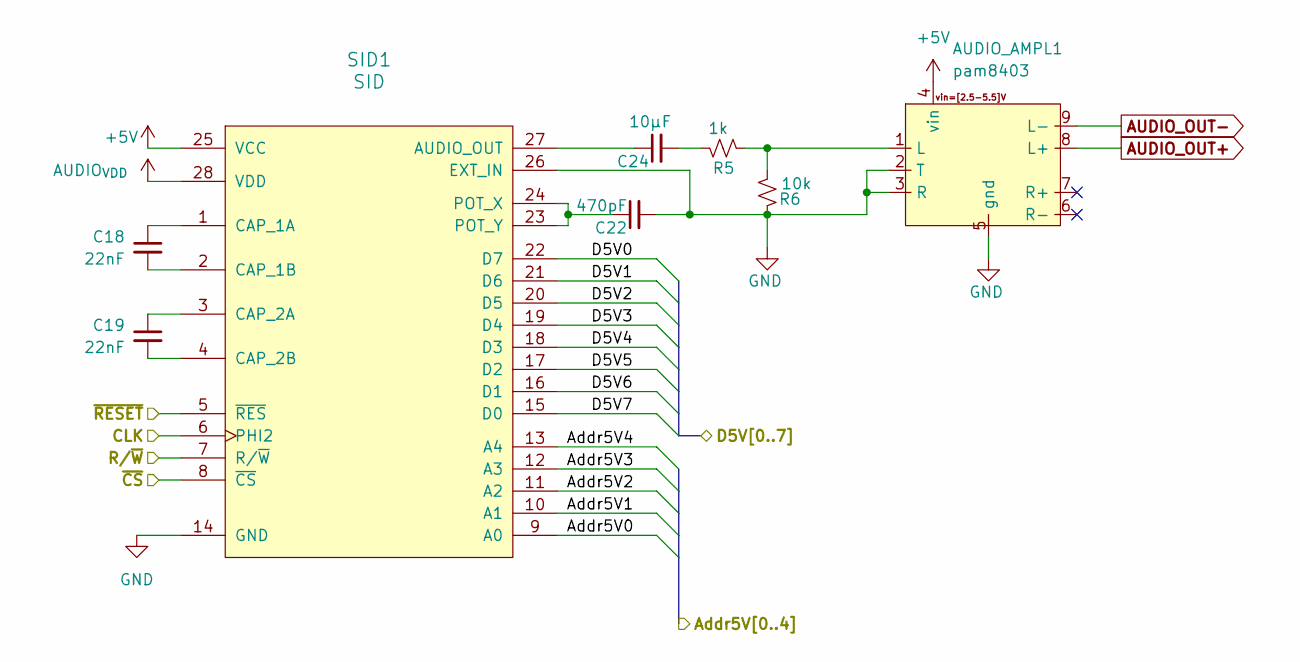
[picture p16: schematic sid.kicad_sch]

Parts:
AUDIO_AMPL1: pam8403
C18, C19: 22nF; C_0603_1608Metric; PartNumber CL10B104KB8NNNC
C22: 470pF; C_0603_1608Metric; PartNumber CL10B104KB8NNNC
C24: 10µF; C_0603_1608Metric; PartNumber CL10B104KB8NNNC
R5: 1k; R_0603_1608Metric; PartNumber RC0603FR-0712K4L
R6: 10k; R_0603_1608Metric; PartNumber RC0603FR-0712K4L
SID1: SID; DIP-28_W15.24mm_Socket

Connections:
+5V: AUDIO_AMPL1.4 (vin), SID1.25 (VCC)
AUDIO_OUT+: AUDIO_AMPL1.8 (L+)
AUDIO_OUT-: AUDIO_AMPL1.9 (L-)
AUDIO_{VDD}: SID1.28 (VDD)
Addr5V0: SID1.9 (A0)
Addr5V1: SID1.10 (A1)
Addr5V2: SID1.11 (A2)
Addr5V3: SID1.12 (A3)
Addr5V4: SID1.13 (A4)
CLK: SID1.6 (PHI2)
D5V0: SID1.22 (D7)
D5V1: SID1.21 (D6)
D5V2: SID1.20 (D5)
D5V3: SID1.19 (D4)
D5V4: SID1.18 (D3)
D5V5: SID1.17 (D2)
D5V6: SID1.16 (D1)
D5V7: SID1.15 (D0)
GND: AUDIO_AMPL1.2 (T), AUDIO_AMPL1.3 (R), AUDIO_AMPL1.5 (gnd), C22.2, R6.2, SID1.14 (GND), SID1.26 (EXT_IN)
unnamed: AUDIO_AMPL1.1 (L), R5.1, R6.1
unnamed: C18.1, SID1.1 (CAP_1A)
unnamed: C18.2, SID1.2 (CAP_1B)
unnamed: C19.1, SID1.3 (CAP_2A)
unnamed: C19.2, SID1.4 (CAP_2B)
unnamed: C22.1, SID1.23 (POT_Y), SID1.24 (POT_X)
unnamed: C24.1, SID1.27 (AUDIO_OUT)
unnamed: C24.2, R5.2
R/~W: SID1.7 (R/~W)
~CS: SID1.8 (~CS)
~RESET: SID1.5 (~RES)
