Apoll011/Lambda-One/hardware/spi.kicad_sch

## KiCad design hardware/spi.kicad_sch (2026-07-18)

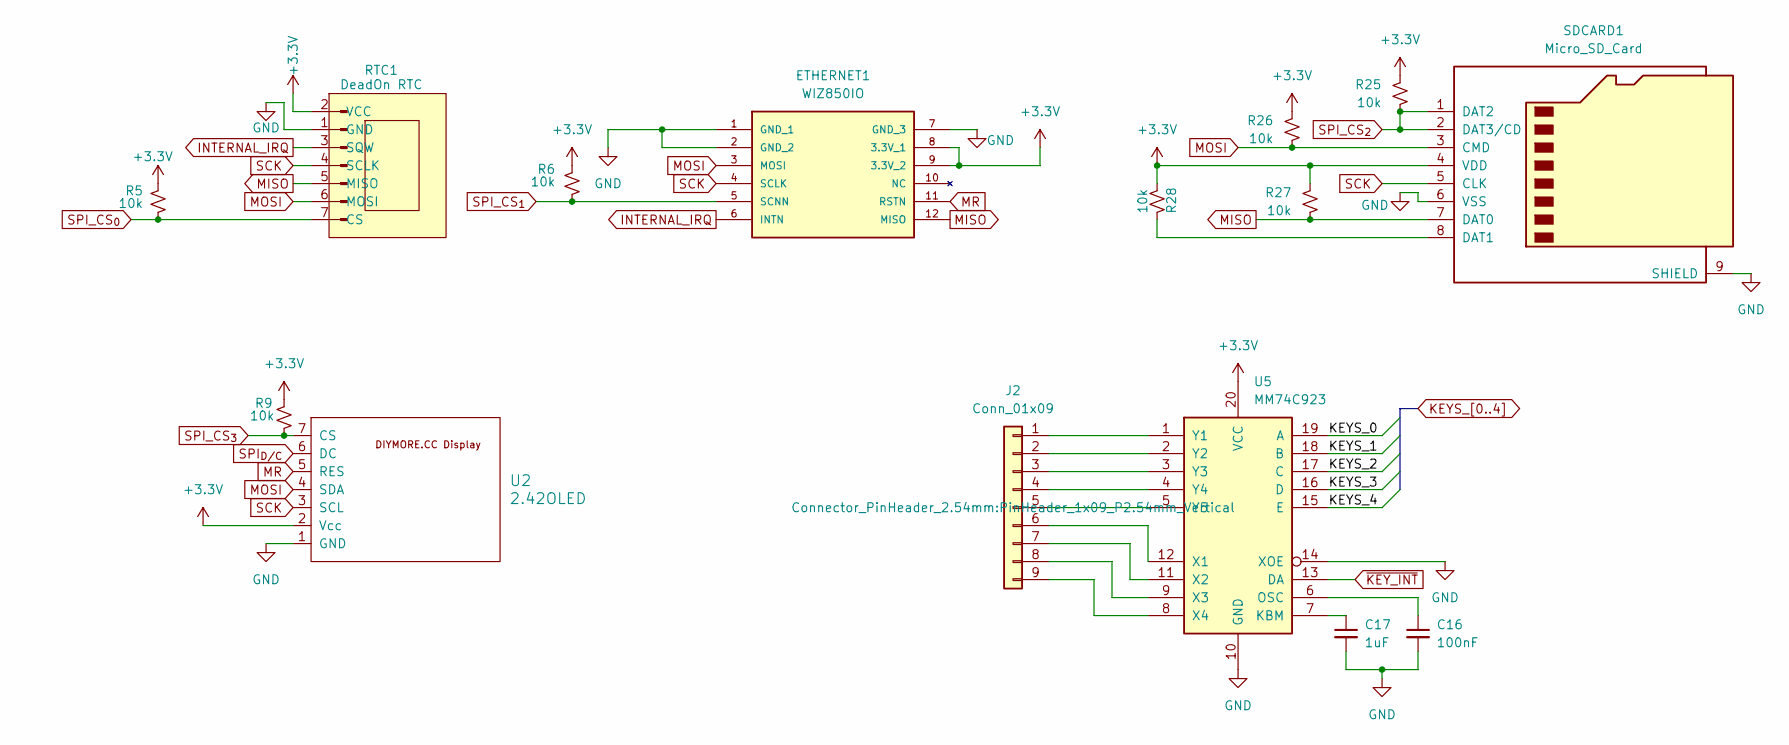
[picture p17: schematic spi.kicad_sch]

Parts:
C16: 100nF; C_0603_1608Metric; PartNumber CL10B104KB8NNNC
C17: 1uF; C_0603_1608Metric; PartNumber CL10A105KB8NNNC
ETHERNET1: WIZ850IO
J2: Conn_01x09; PinHeader_1x09_P2.54mm_Vertical
R5, R6, R9, R25, R26, R27, R28: 10k; R_0603_1608Metric; PartNumber AC0603JR-0710KL
RTC1: DeadOn RTC; PinHeader_1x07_P2.54mm_Vertical
SDCARD1: Micro_SD_Card; SIP-9_22.3x3mm_P2.54mm
U2: 2.42OLED; DIYMORE.CC
U5: MM74C923; DIP-20_W7.62mm

Connections:
+3.3V: ETHERNET1.8 (3.3V_1), ETHERNET1.9 (3.3V_2), R5.1, R6.1, R9.1, R25.1, R26.1, R27.1, R28.1, RTC1.2 (VCC), SDCARD1.4 (VDD), U2.2 (Vcc), U5.20 (VCC)
GND: C16.2, C17.2, ETHERNET1.1 (GND_1), ETHERNET1.2 (GND_2), ETHERNET1.7 (GND_3), RTC1.1 (GND), SDCARD1.6 (VSS), SDCARD1.9 (SHIELD), U2.1 (GND), U5.10 (GND), U5.14 (XOE)
INTERNAL_IRQ: ETHERNET1.6 (INTN), RTC1.3 (SQW)
KEYS_0: U5.19 (A)
KEYS_1: U5.18 (B)
KEYS_2: U5.17 (C)
KEYS_3: U5.16 (D)
KEYS_4: U5.15 (E)
MISO: ETHERNET1.12 (MISO), R27.2, RTC1.5 (MISO), SDCARD1.7 (DAT0)
MOSI: ETHERNET1.3 (MOSI), R26.2, RTC1.6 (MOSI), SDCARD1.3 (CMD), U2.4 (SDA)
MR: ETHERNET1.11 (RSTN), U2.5 (RES)
unnamed: C16.1, U5.6 (OSC)
unnamed: C17.1, U5.7 (KBM)
unnamed: J2.1, U5.1 (Y1)
unnamed: J2.2, U5.2 (Y2)
unnamed: J2.3, U5.3 (Y3)
unnamed: J2.4, U5.4 (Y4)
unnamed: J2.5, U5.5 (Y5)
unnamed: J2.6, U5.12 (X1)
unnamed: J2.7, U5.11 (X2)
unnamed: J2.8, U5.9 (X3)
unnamed: J2.9, U5.8 (X4)
unnamed: R28.2, SDCARD1.8 (DAT1)
SCK: ETHERNET1.4 (SCLK), RTC1.4 (SCLK), SDCARD1.5 (CLK), U2.3 (SCL)
SPI_CS_{0}: R5.2, RTC1.7 (CS)
SPI_CS_{1}: ETHERNET1.5 (SCNN), R6.2
SPI_CS_{2}: R25.2, SDCARD1.1 (DAT2), SDCARD1.2 (DAT3/CD)
SPI_CS_{3}: R9.2, U2.7 (CS)
SPI_{D/C}: U2.6 (DC)
~KEY_INT: U5.13 (DA)
