Apoll011/Lambda-One/hardware/va.kicad_sch

## KiCad design hardware/va.kicad_sch (2026-07-18)

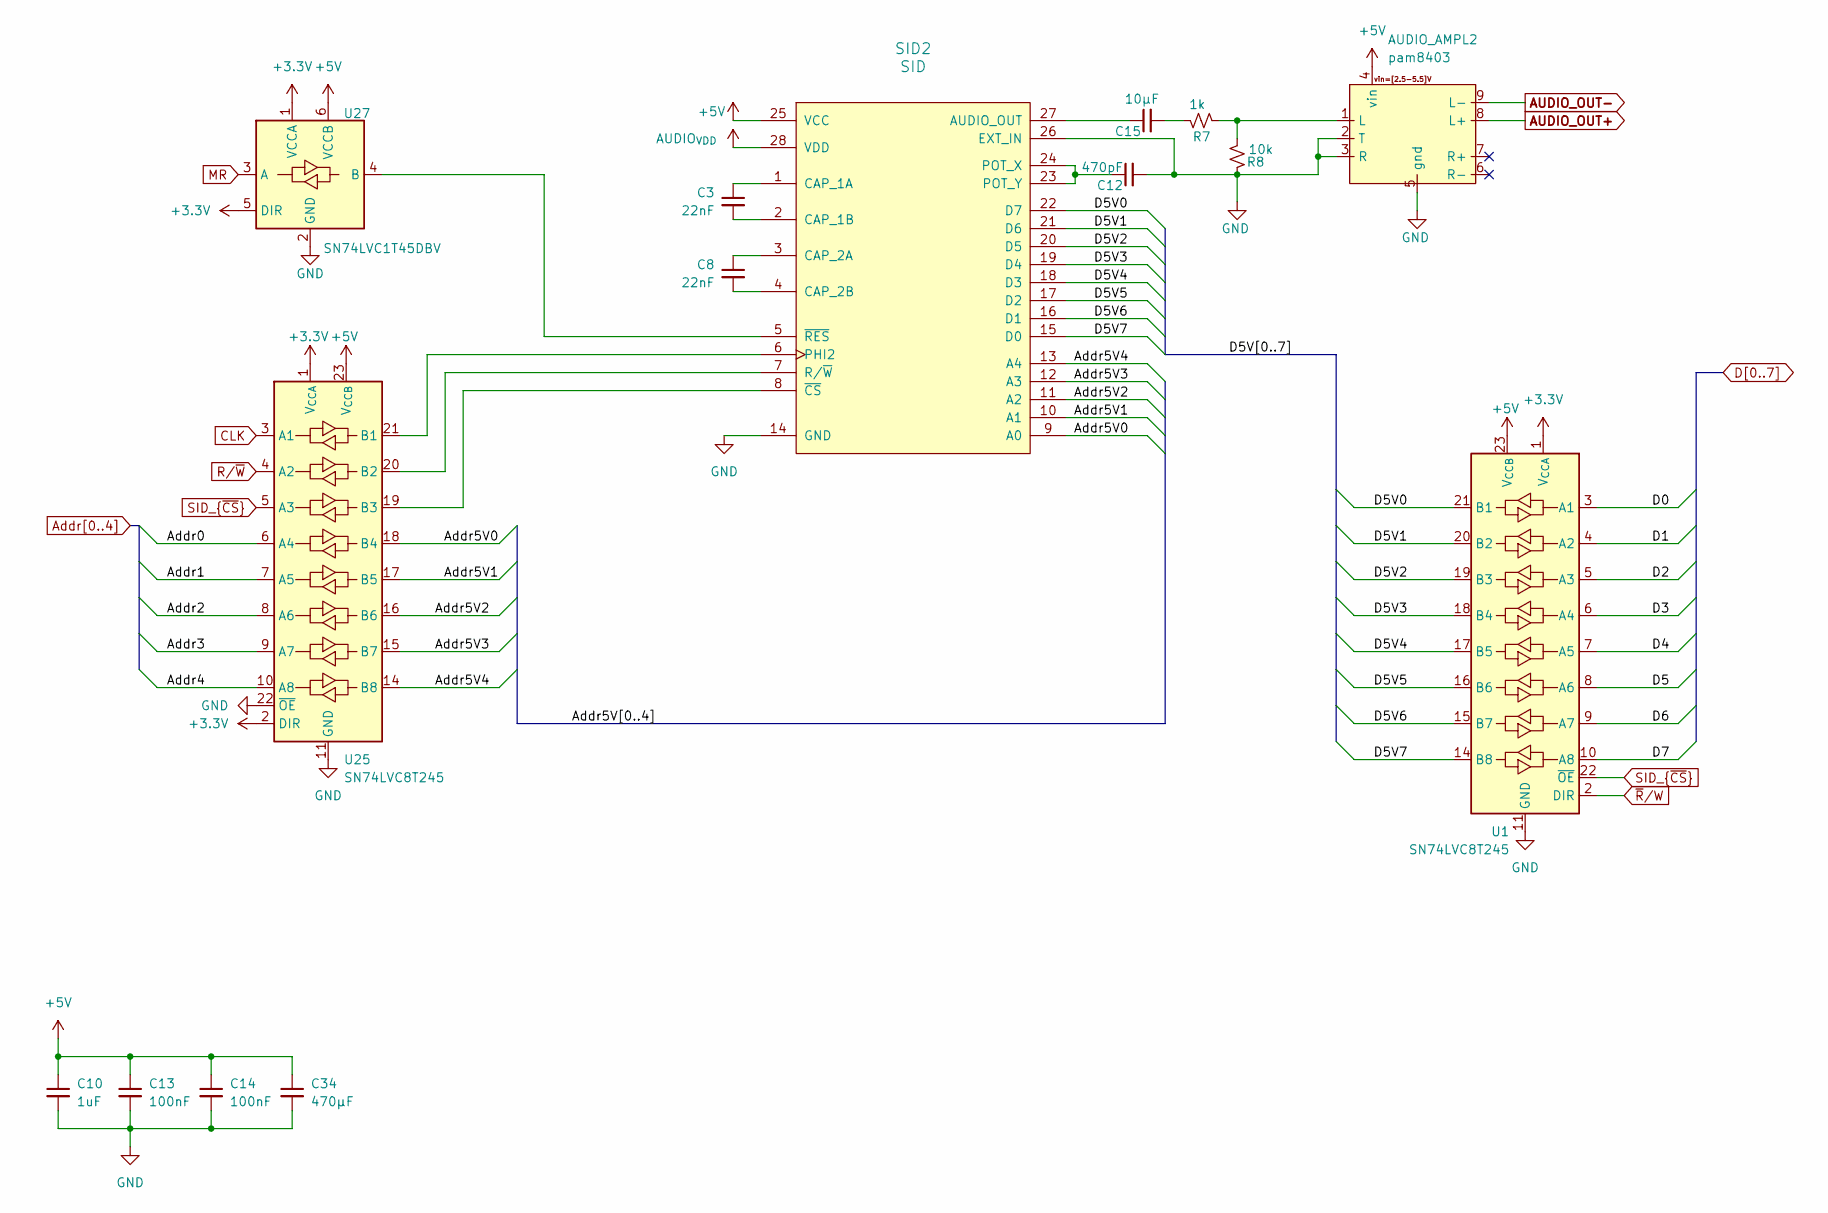
[picture p18: schematic va.kicad_sch]

Parts:
AUDIO_AMPL2: pam8403
C3, C8: 22nF; C_0603_1608Metric; PartNumber CL10B104KB8NNNC
C10: 1uF; C_0603_1608Metric; PartNumber CL10A105KB8NNNC
C12: 470pF; C_0603_1608Metric; PartNumber CL10B104KB8NNNC
C13, C14: 100nF; C_0603_1608Metric; PartNumber CL10B104KB8NNNC
C15: 10µF; C_0603_1608Metric; PartNumber CL10B104KB8NNNC
C34: 470µF; Fuse_Bourns_MF-RG1000; PartNumber CL10B104KB8NNNC
R7: 1k; R_0603_1608Metric; PartNumber RC0603FR-0712K4L
R8: 10k; R_0603_1608Metric; PartNumber RC0603FR-0712K4L
SID2: SID; DIP-28_W15.24mm_Socket
U1, U25: SN74LVC8T245; SSOP-24_3.9x8.7mm_P0.635mm
U27: SN74LVC1T45DBV; SOT-23-6

Connections:
+3.3V: U1.1 (V_{CCA}), U25.1 (V_{CCA}), U25.2 (DIR), U27.1 (VCCA), U27.5 (DIR)
+5V: AUDIO_AMPL2.4 (vin), C10.1, C13.1, C14.1, C34.1, SID2.25 (VCC), U1.23 (V_{CCB}), U1.24 (V_{CCB}), U25.23 (V_{CCB}), U25.24 (V_{CCB}), U27.6 (VCCB)
AUDIO_OUT+: AUDIO_AMPL2.8 (L+)
AUDIO_OUT-: AUDIO_AMPL2.9 (L-)
AUDIO_{VDD}: SID2.28 (VDD)
Addr0: U25.6 (A4)
Addr1: U25.7 (A5)
Addr2: U25.8 (A6)
Addr3: U25.9 (A7)
Addr4: U25.10 (A8)
Addr5V0: SID2.9 (A0), U25.18 (B4)
Addr5V1: SID2.10 (A1), U25.17 (B5)
Addr5V2: SID2.11 (A2), U25.16 (B6)
Addr5V3: SID2.12 (A3), U25.15 (B7)
Addr5V4: SID2.13 (A4), U25.14 (B8)
CLK: U25.3 (A1)
D0: U1.3 (A1)
D1: U1.4 (A2)
D2: U1.5 (A3)
D3: U1.6 (A4)
D4: U1.7 (A5)
D5: U1.8 (A6)
D5V0: SID2.22 (D7), U1.21 (B1)
D5V1: SID2.21 (D6), U1.20 (B2)
D5V2: SID2.20 (D5), U1.19 (B3)
D5V3: SID2.19 (D4), U1.18 (B4)
D5V4: SID2.18 (D3), U1.17 (B5)
D5V5: SID2.17 (D2), U1.16 (B6)
D5V6: SID2.16 (D1), U1.15 (B7)
D5V7: SID2.15 (D0), U1.14 (B8)
D6: U1.9 (A7)
D7: U1.10 (A8)
GND: AUDIO_AMPL2.2 (T), AUDIO_AMPL2.3 (R), AUDIO_AMPL2.5 (gnd), C10.2, C12.2, C13.2, C14.2, C34.2, R8.2, SID2.14 (GND), SID2.26 (EXT_IN), U1.11 (GND), U1.12 (GND), U1.13 (GND), U25.11 (GND), U25.12 (GND), U25.13 (GND), U25.22 (~OE), U27.2 (GND)
MR: U27.3 (A)
unnamed: AUDIO_AMPL2.1 (L), R7.1, R8.1
unnamed: C3.1, SID2.1 (CAP_1A)
unnamed: C3.2, SID2.2 (CAP_1B)
unnamed: C8.1, SID2.3 (CAP_2A)
unnamed: C8.2, SID2.4 (CAP_2B)
unnamed: C12.1, SID2.23 (POT_Y), SID2.24 (POT_X)
unnamed: C15.1, SID2.27 (AUDIO_OUT)
unnamed: C15.2, R7.2
unnamed: SID2.5 (~RES), U27.4 (B)
unnamed: SID2.6 (PHI2), U25.21 (B1)
unnamed: SID2.7 (R/~W), U25.20 (B2)
unnamed: SID2.8 (~CS), U25.19 (B3)
R/~W: U25.4 (A2)
SID_{~CS}: U1.22 (~OE), U25.5 (A3)
~R/W: U1.2 (DIR)
