Apoll011/Lambda-One/hardware/video.kicad_sch

## KiCad design hardware/video.kicad_sch (2026-07-14)

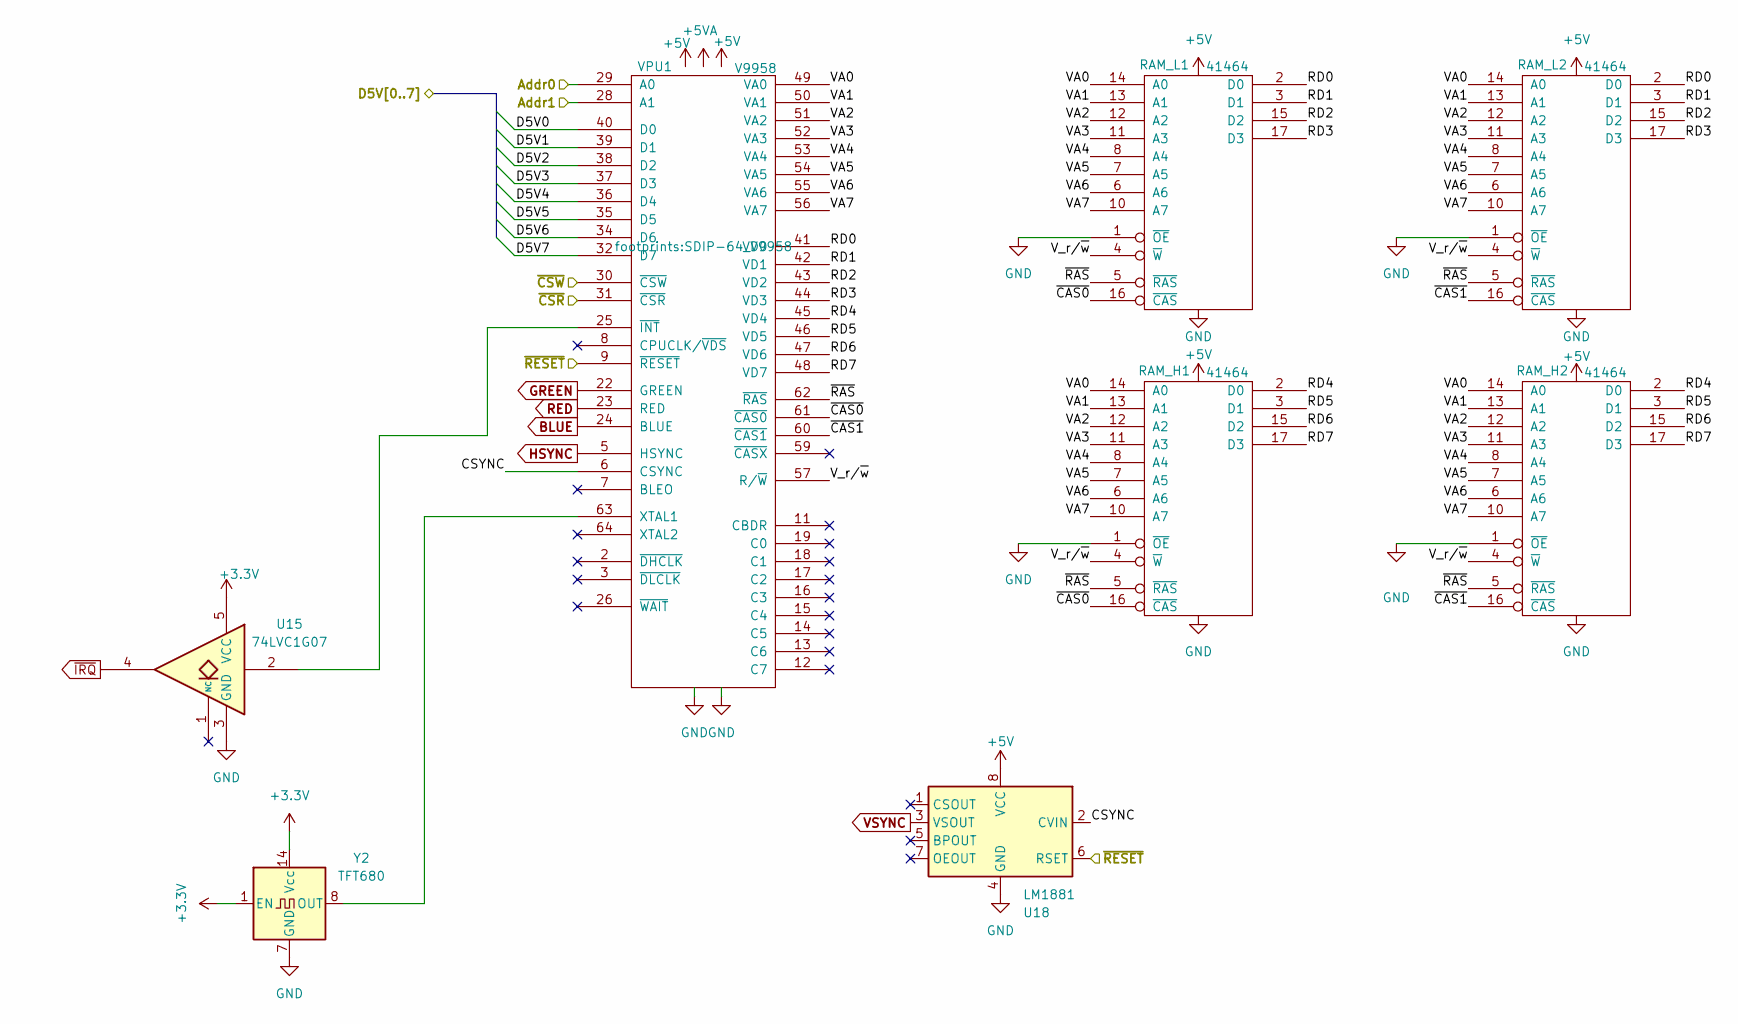
[picture p19: schematic video.kicad_sch]

Parts:
RAM_H1, RAM_H2: 41464; DIP-18_W7.62mm
RAM_L1, RAM_L2: 41464; DIP-18_W7.62mm
U15: 74LVC1G07; SOT-23-5
U18: LM1881; DIP-8_W7.62mm
VPU1: V9958; SDIP-64_V9958
Y2: TFT680; Oscillator_DIP-14

Connections:
+3.3V: U15.5 (VCC), Y2.1 (EN), Y2.14 (Vcc)
+5V: RAM_H1.9 (VCC), RAM_H2.9 (VCC), RAM_L1.9 (VCC), RAM_L2.9 (VCC), U18.8 (VCC), VPU1.33 (Vbb), VPU1.58 (VCC)
+5VA: VPU1.21 (VDD)
Addr0: VPU1.29 (A0)
Addr1: VPU1.28 (A1)
BLUE: VPU1.24 (BLUE)
CSYNC: U18.2 (CVIN), VPU1.6 (CSYNC)
D5V0: VPU1.40 (D0)
D5V1: VPU1.39 (D1)
D5V2: VPU1.38 (D2)
D5V3: VPU1.37 (D3)
D5V4: VPU1.36 (D4)
D5V5: VPU1.35 (D5)
D5V6: VPU1.34 (D6)
D5V7: VPU1.32 (D7)
GND: RAM_H1.1 (~OE), RAM_H1.18 (GND), RAM_H2.1 (~OE), RAM_H2.18 (GND), RAM_L1.1 (~OE), RAM_L1.18 (GND), RAM_L2.1 (~OE), RAM_L2.18 (GND), U15.3 (GND), U18.4 (GND), VPU1.1 (GND), VPU1.20 (GND), Y2.7 (GND)
GREEN: VPU1.22 (GREEN)
HSYNC: VPU1.5 (HSYNC)
unnamed: U15.2, VPU1.25 (~INT)
unnamed: VPU1.63 (XTAL1), Y2.8 (OUT)
RD0: RAM_L1.2 (D0), RAM_L2.2 (D0), VPU1.41 (VD0)
RD1: RAM_L1.3 (D1), RAM_L2.3 (D1), VPU1.42 (VD1)
RD2: RAM_L1.15 (D2), RAM_L2.15 (D2), VPU1.43 (VD2)
RD3: RAM_L1.17 (D3), RAM_L2.17 (D3), VPU1.44 (VD3)
RD4: RAM_H1.2 (D0), RAM_H2.2 (D0), VPU1.45 (VD4)
RD5: RAM_H1.3 (D1), RAM_H2.3 (D1), VPU1.46 (VD5)
RD6: RAM_H1.15 (D2), RAM_H2.15 (D2), VPU1.47 (VD6)
RD7: RAM_H1.17 (D3), RAM_H2.17 (D3), VPU1.48 (VD7)
RED: VPU1.23 (RED)
VA0: RAM_H1.14 (A0), RAM_H2.14 (A0), RAM_L1.14 (A0), RAM_L2.14 (A0), VPU1.49 (VA0)
VA1: RAM_H1.13 (A1), RAM_H2.13 (A1), RAM_L1.13 (A1), RAM_L2.13 (A1), VPU1.50 (VA1)
VA2: RAM_H1.12 (A2), RAM_H2.12 (A2), RAM_L1.12 (A2), RAM_L2.12 (A2), VPU1.51 (VA2)
VA3: RAM_H1.11 (A3), RAM_H2.11 (A3), RAM_L1.11 (A3), RAM_L2.11 (A3), VPU1.52 (VA3)
VA4: RAM_H1.8 (A4), RAM_H2.8 (A4), RAM_L1.8 (A4), RAM_L2.8 (A4), VPU1.53 (VA4)
VA5: RAM_H1.7 (A5), RAM_H2.7 (A5), RAM_L1.7 (A5), RAM_L2.7 (A5), VPU1.54 (VA5)
VA6: RAM_H1.6 (A6), RAM_H2.6 (A6), RAM_L1.6 (A6), RAM_L2.6 (A6), VPU1.55 (VA6)
VA7: RAM_H1.10 (A7), RAM_H2.10 (A7), RAM_L1.10 (A7), RAM_L2.10 (A7), VPU1.56 (VA7)
VSYNC: U18.3 (VSOUT)
V_r/~w: RAM_H1.4 (~W), RAM_H2.4 (~W), RAM_L1.4 (~W), RAM_L2.4 (~W), VPU1.57 (R/~W)
~CAS0: RAM_H1.16 (~CAS), RAM_L1.16 (~CAS), VPU1.61 (~CAS0)
~CAS1: RAM_H2.16 (~CAS), RAM_L2.16 (~CAS), VPU1.60 (~CAS1)
~CSR: VPU1.31 (~CSR)
~CSW: VPU1.30 (~CSW)
~IRQ: U15.4
~RAS: RAM_H1.5 (~RAS), RAM_H2.5 (~RAS), RAM_L1.5 (~RAS), RAM_L2.5 (~RAS), VPU1.62 (~RAS)
~RESET: U18.6 (RSET), VPU1.9 (~RESET)
